FoosTronics/Main_program/Extra/Doxygen documentatie/html/promo.jpg

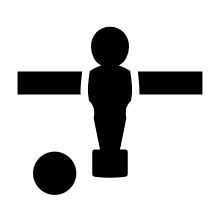
Extra/Doxygen documentatie/html/promo.jpg
