FoosTronics/Main_program/Extra/Promo/Afbeeldingen/voorkant_tafel.jpg

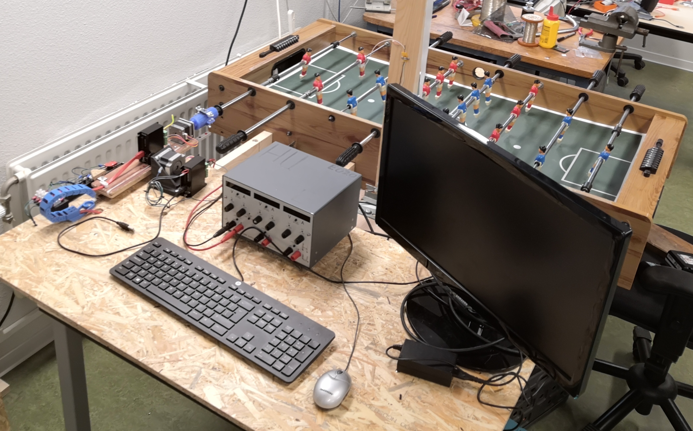
Extra/Promo/Afbeeldingen/voorkant_tafel.jpg
