FoosTronics/Main_program/Extra/Promo/promo.jpg

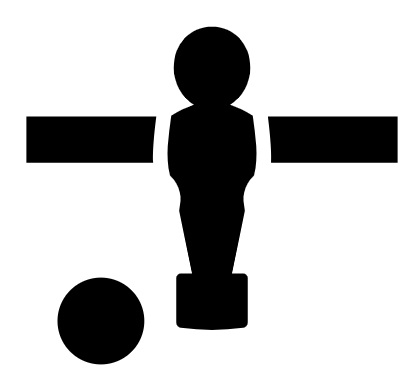
Extra/Promo/promo.jpg
