FoosTronics/Main_program/Extra/3D-tekeningen/AssembliesEtc/lens.SLDPRT

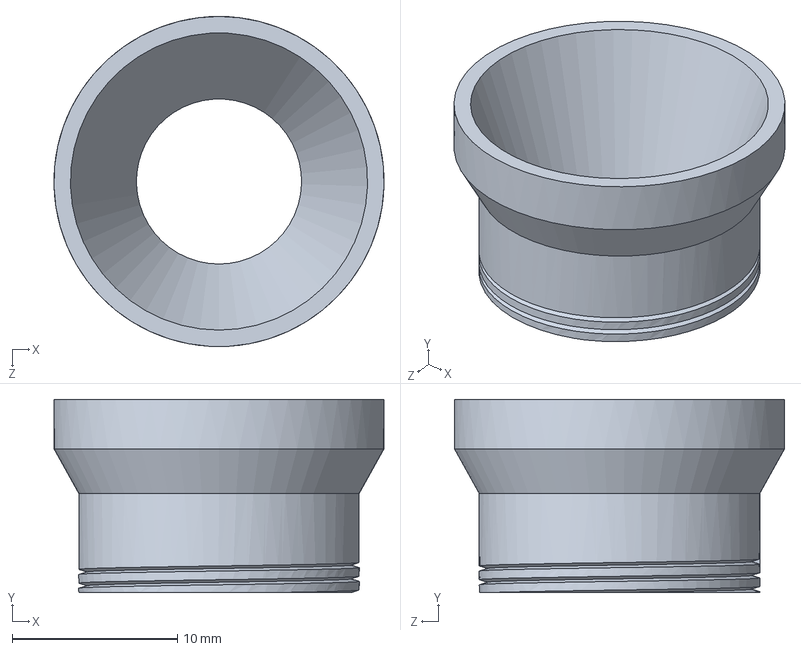
[picture p75: CAD file, 2020-01-23]
Extra/3D-tekeningen/AssembliesEtc/lens.SLDPRT
20.0 x 11.7 x 20.0 mm
