FoosTronics/Main_program/Extra/3D-models/Eindschakelaarbord.stl

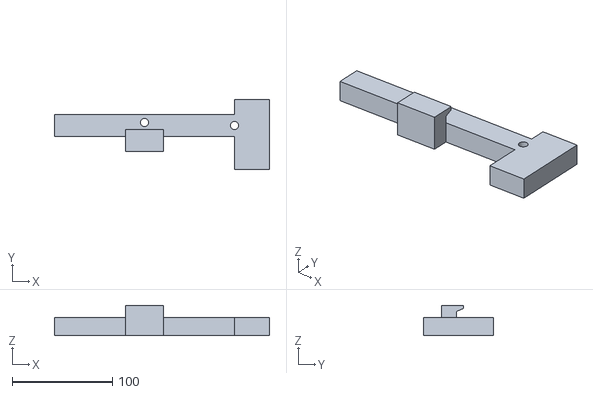
[picture p76: CAD file, 2020-01-23]
Extra/3D-models/Eindschakelaarbord.stl
215.0 x 70.0 x 30.0
