FoosTronics/Main_program/Extra/3D-models/Grondplaat 1mm.stl

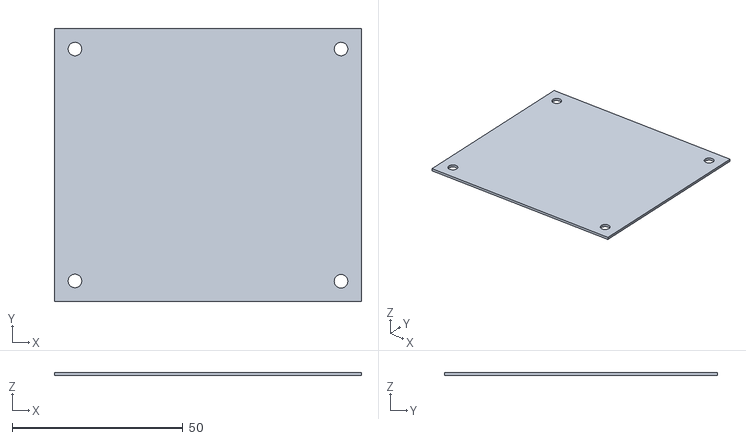
[picture p77: CAD file, 2020-01-23]
Extra/3D-models/Grondplaat 1mm.stl
90.0 x 80.0 x 1.00
